Anayjain1129/aniboard/images/3dcase_front.png

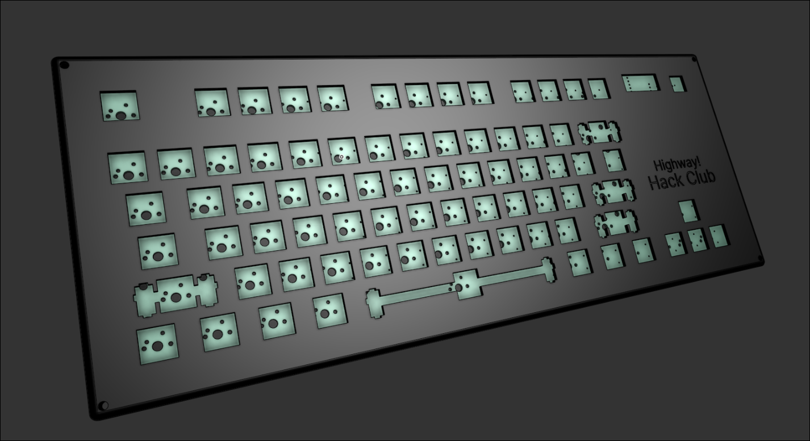
images/3dcase_front.png
